greenjacketgirl/SDR_Receiver/Photos/2 - Bit Counter.png

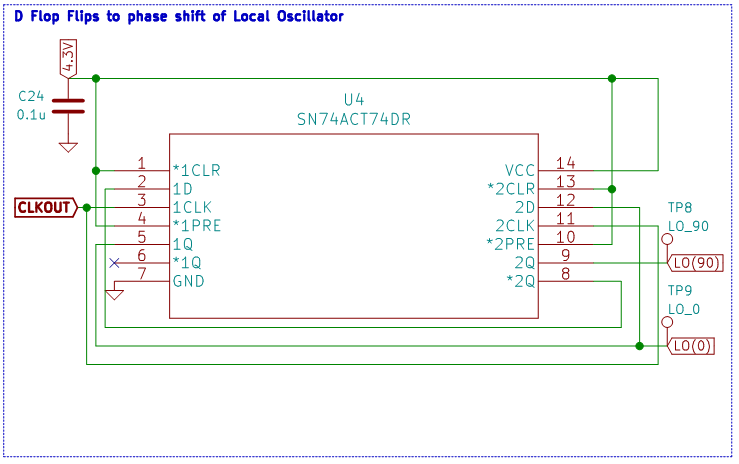
Photos/2 - Bit Counter.png
