greenjacketgirl/SDR_Receiver/Photos/blockdiagramforsdrreceiver.png

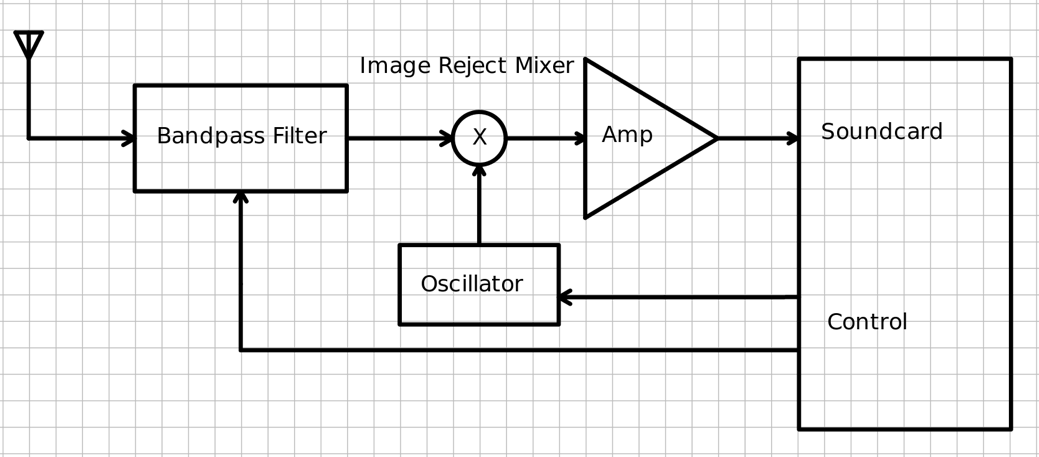
Photos/blockdiagramforsdrreceiver.png
