greenjacketgirl/SDR_Receiver/Photos/IMG_20200519_113151.jpg

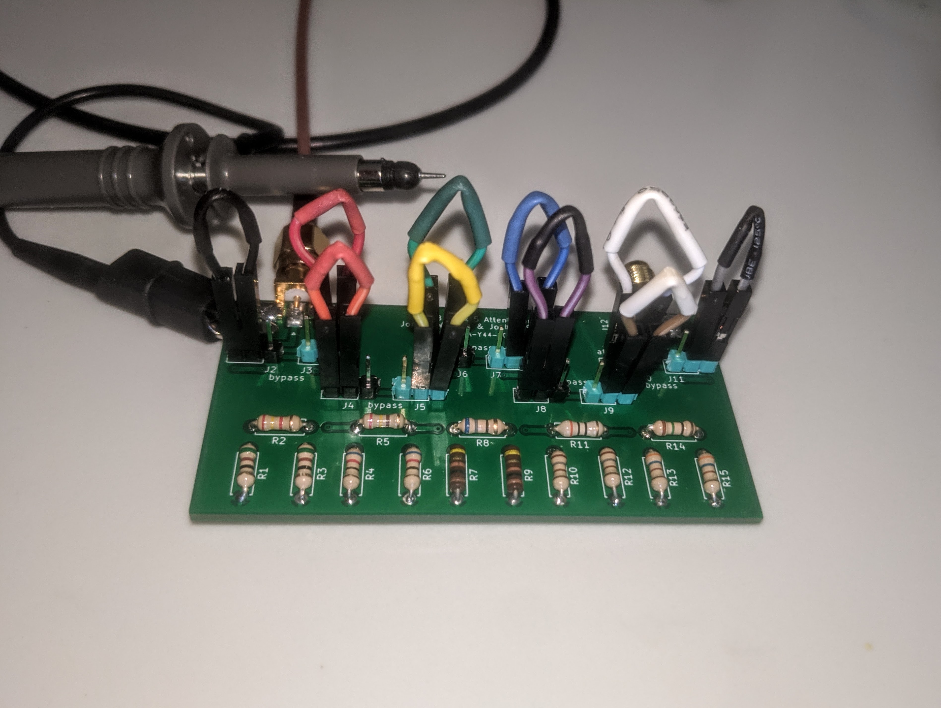
Photos/IMG_20200519_113151.jpg
