greenjacketgirl/SDR_Receiver/Photos/IMG_20200610_005128.jpg

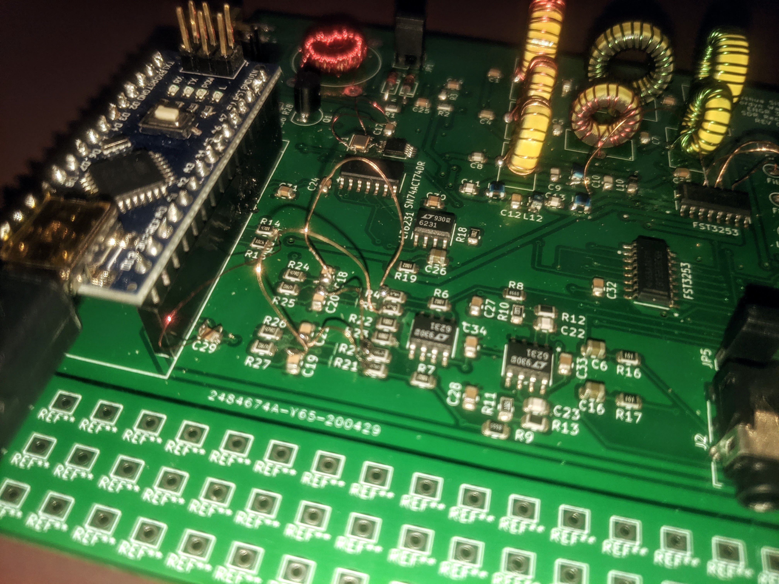
Photos/IMG_20200610_005128.jpg
