greenjacketgirl/SDR_Receiver/Photos/ouputofsummingamps.png

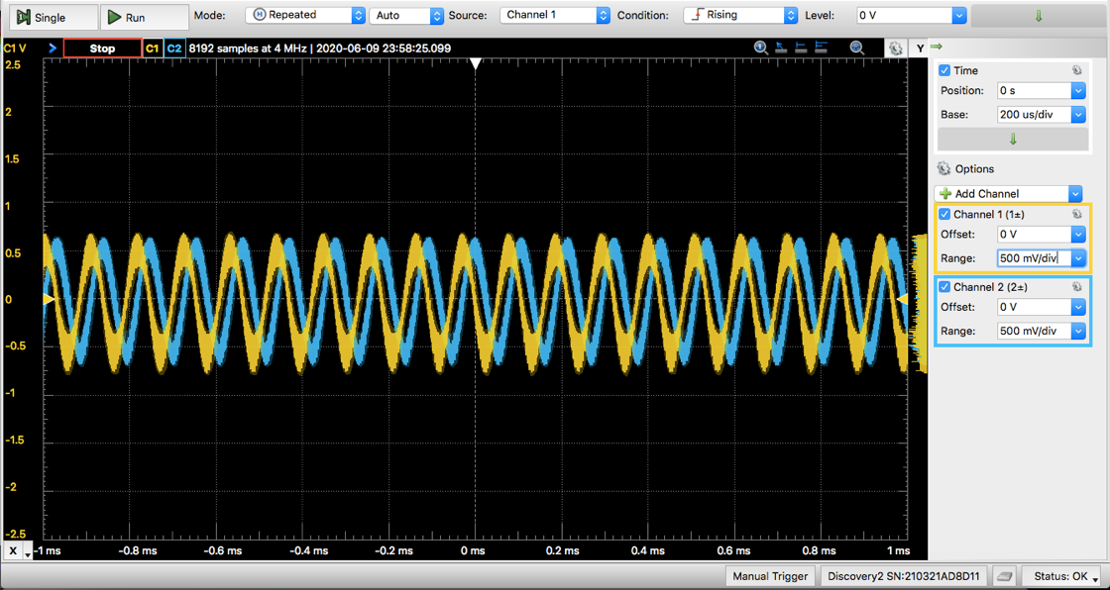
Photos/ouputofsummingamps.png
