greenjacketgirl/SDR_Receiver/Photos/Screenshot 2020-06-01 12.35.27.png

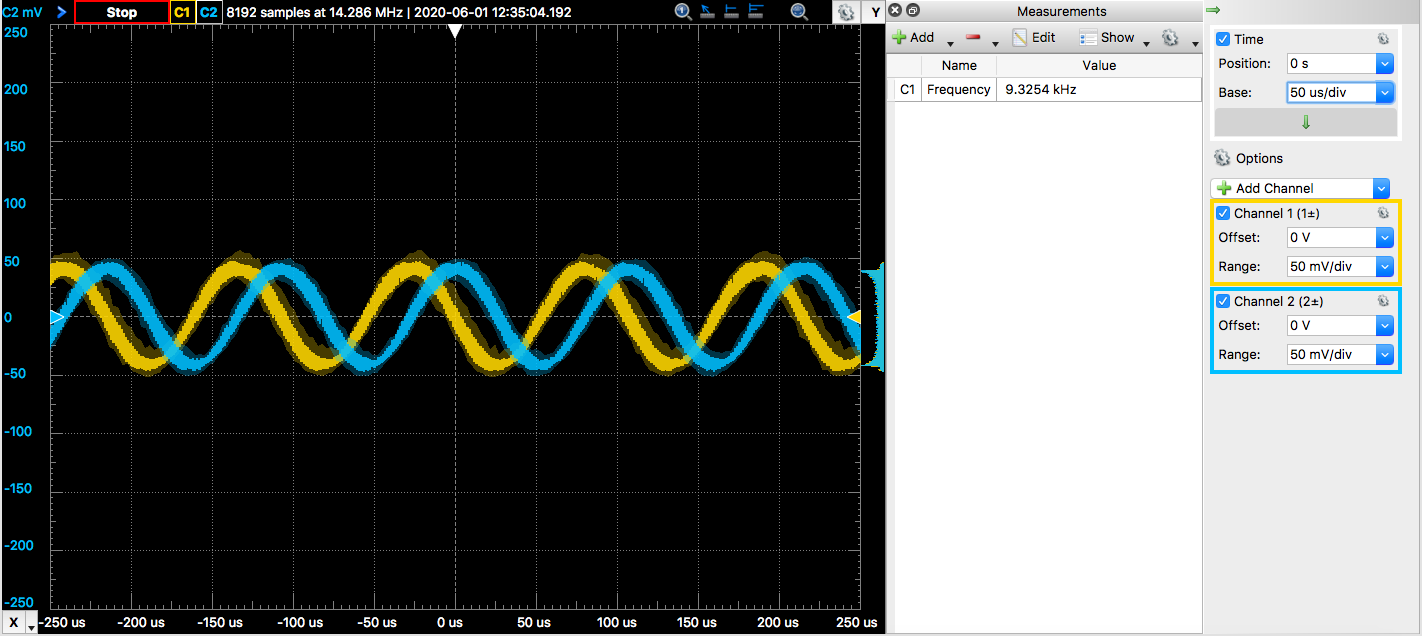
Photos/Screenshot 2020-06-01 12.35.27.png
