greenjacketgirl/SDR_Receiver/Photos/Screenshot 2020-06-01 12.38.04.png

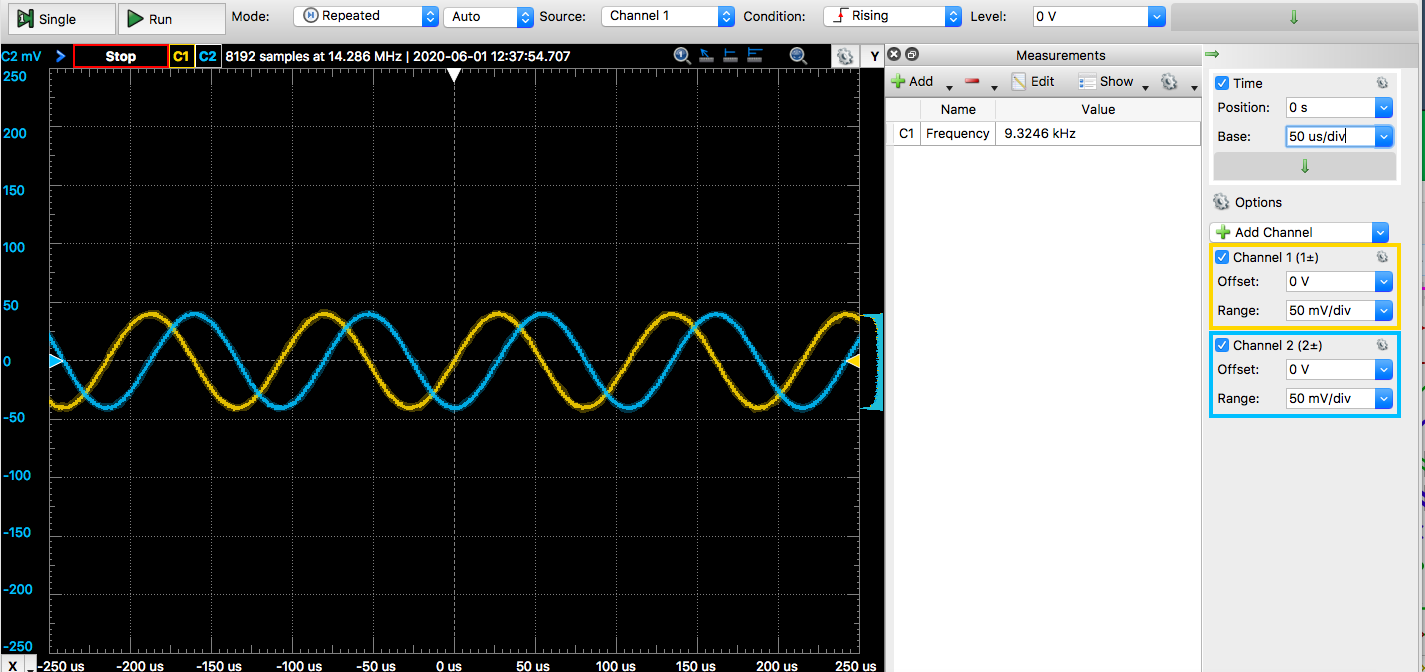
Photos/Screenshot 2020-06-01 12.38.04.png
