greenjacketgirl/SDR_Receiver/Photos/Screenshot 2020-06-01 17.19.47.png

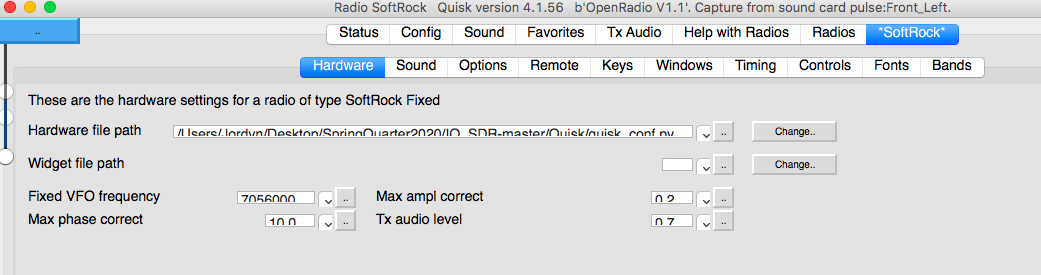
Photos/Screenshot 2020-06-01 17.19.47.png
