greenjacketgirl/SDR_Receiver/Photos/Screenshot 2020-06-03 13.55.31.png

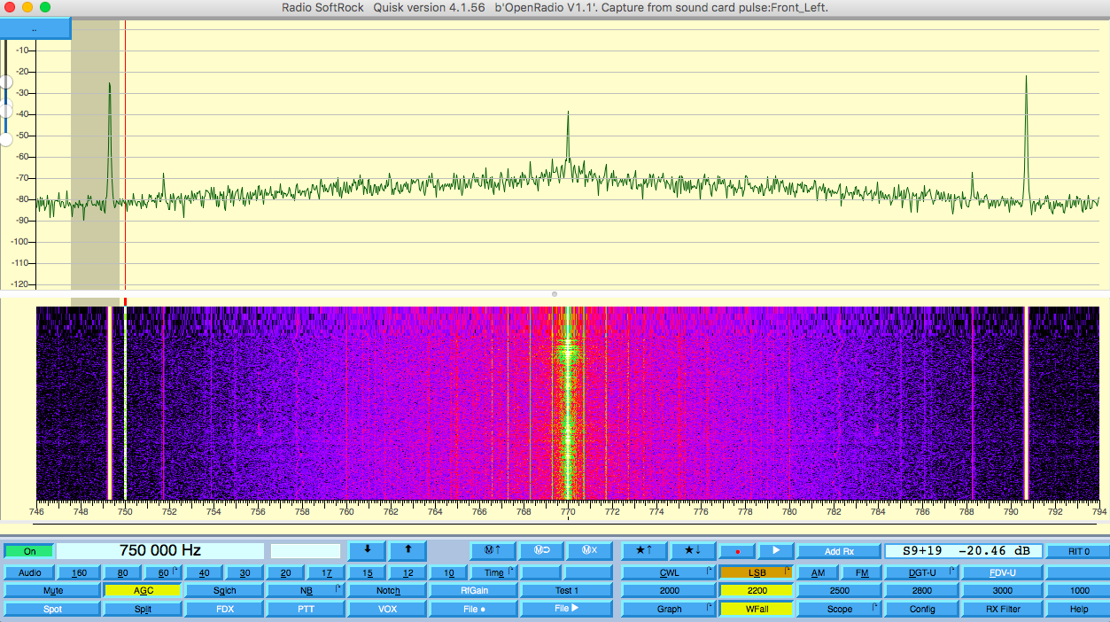
Photos/Screenshot 2020-06-03 13.55.31.png
