greenjacketgirl/SDR_Receiver/Photos/Screenshot 2020-06-03 13.56.09.png

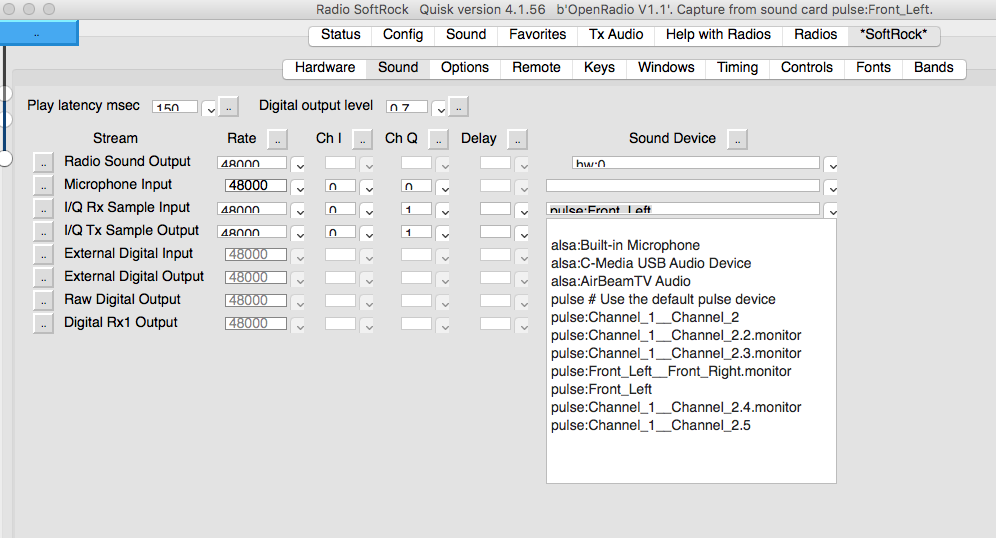
Photos/Screenshot 2020-06-03 13.56.09.png
