greenjacketgirl/SDR_Receiver/Photos/Screenshot 2020-06-05 08.36.38.png

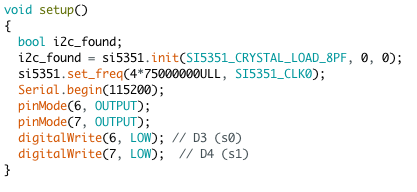
Photos/Screenshot 2020-06-05 08.36.38.png
