greenjacketgirl/SDR_Receiver/Photos/Screenshot 2020-06-09 23.21.12.png

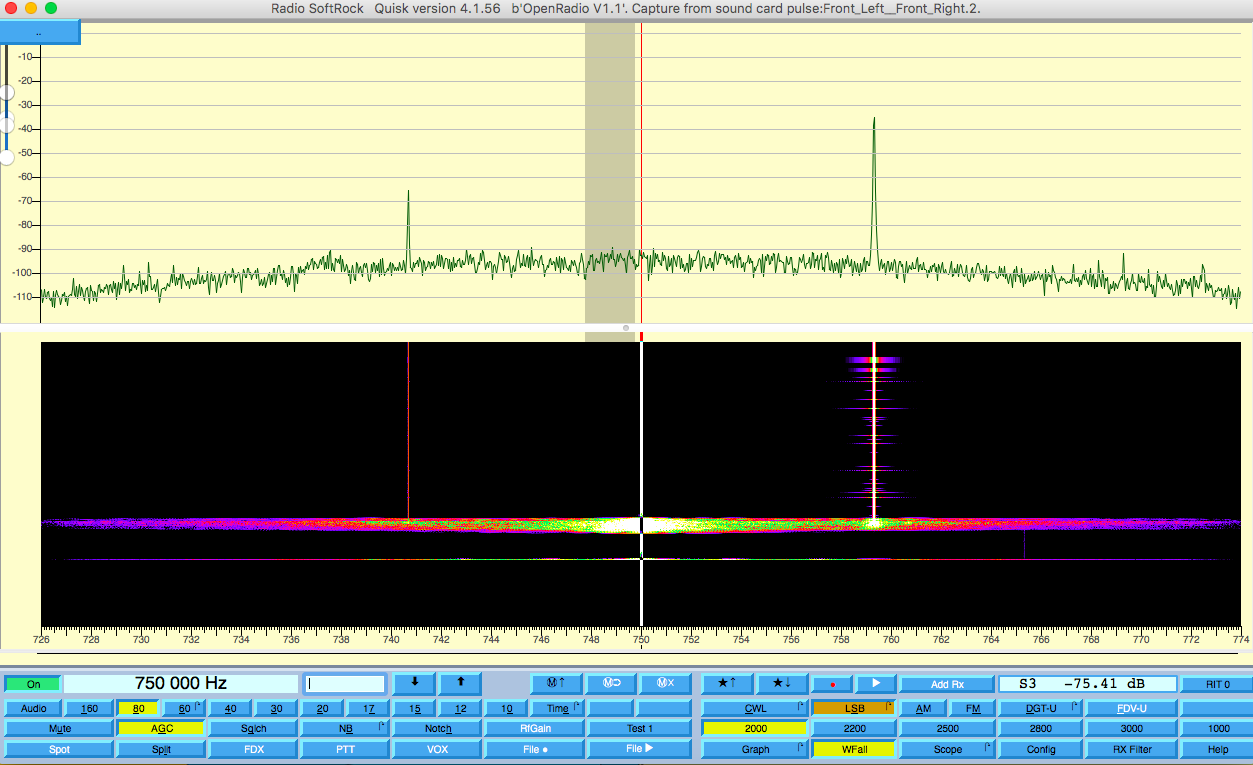
Photos/Screenshot 2020-06-09 23.21.12.png
