greenjacketgirl/SDR_Receiver/Photos/Screenshot 2020-06-09 23.22.24.png

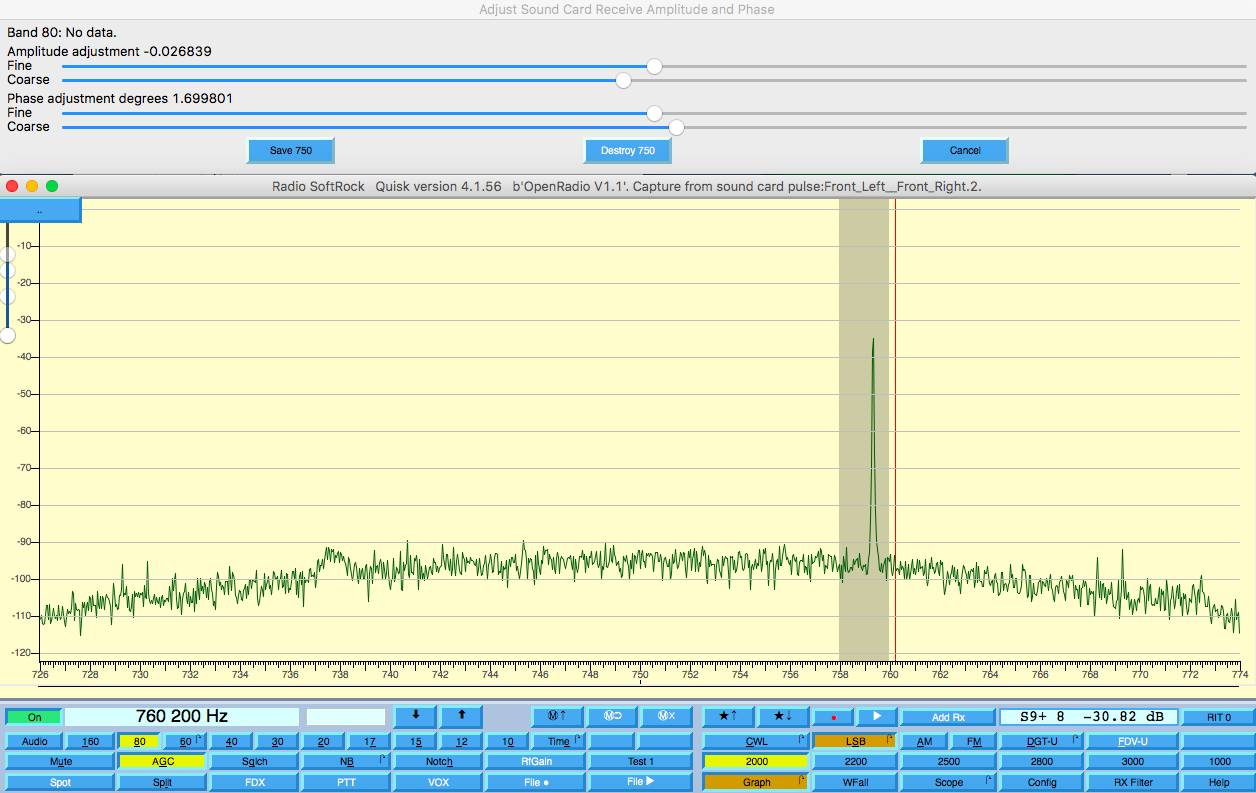
Photos/Screenshot 2020-06-09 23.22.24.png
