greenjacketgirl/SDR_Receiver/Photos/Screenshot 2020-06-09 23.47.44.png

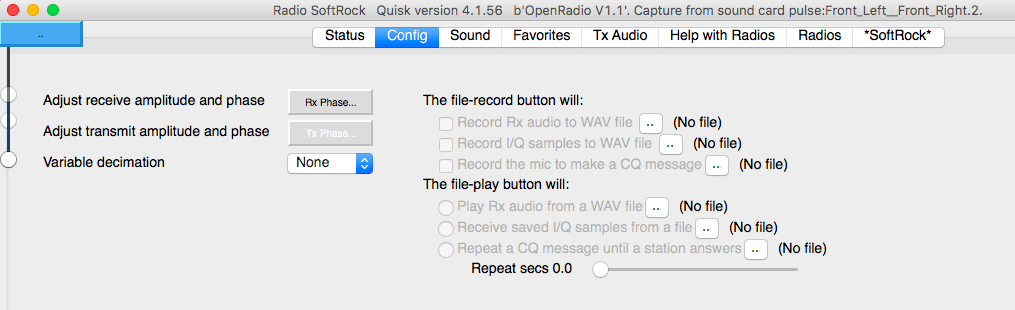
Photos/Screenshot 2020-06-09 23.47.44.png
