greenjacketgirl/SDR_Receiver/Photos/Screenshot 2020-06-09 23.48.01.png

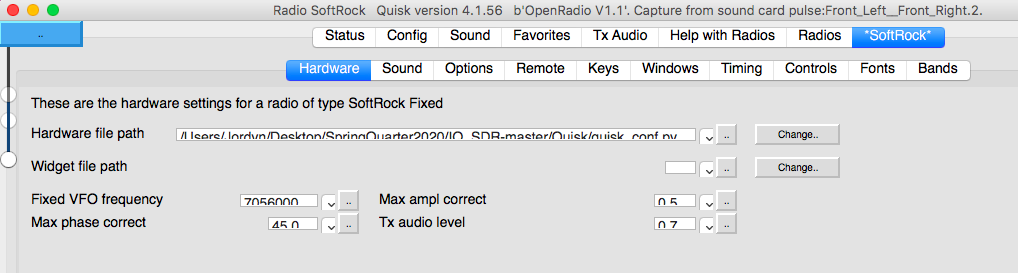
Photos/Screenshot 2020-06-09 23.48.01.png
