greenjacketgirl/SDR_Receiver/Photos/Screenshot 2020-06-10 01.20.28.png

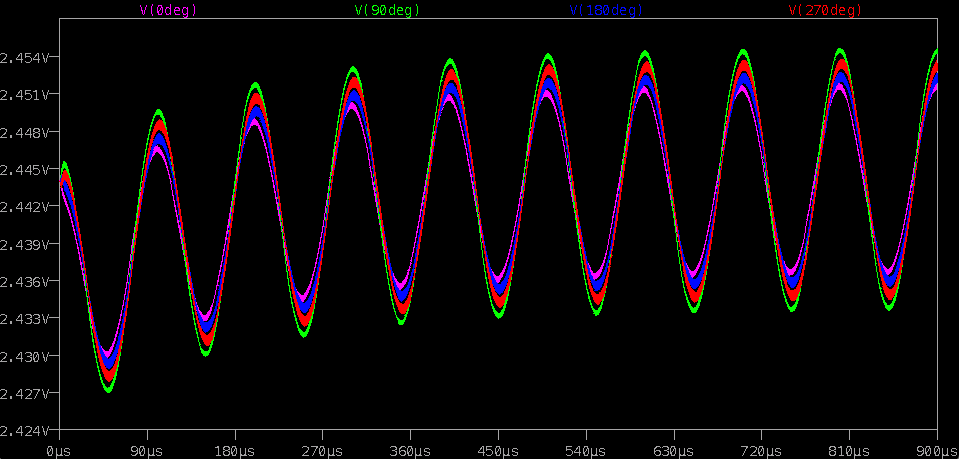
Photos/Screenshot 2020-06-10 01.20.28.png
