greenjacketgirl/SDR_Receiver/Photos/Screenshot 2020-06-10 01.23.52.png

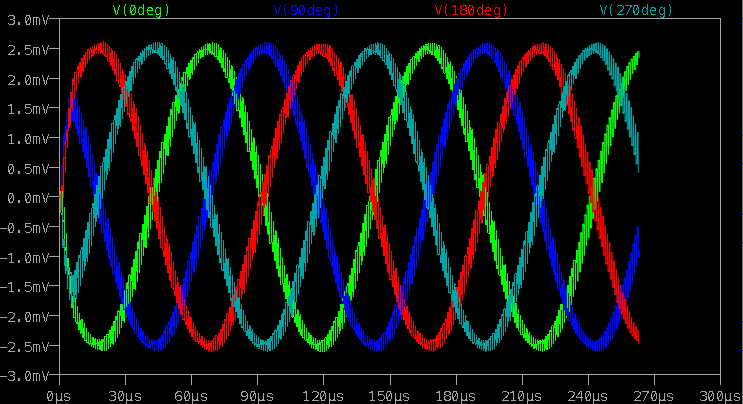
Photos/Screenshot 2020-06-10 01.23.52.png
