greenjacketgirl/SDR_Receiver/Photos/Screenshot 2020-06-11 00.47.50.png

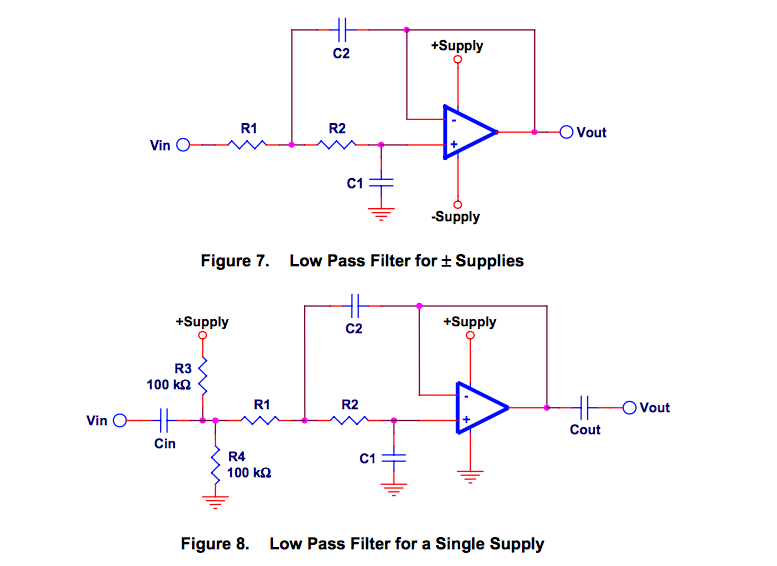
Photos/Screenshot 2020-06-11 00.47.50.png
