greenjacketgirl/SDR_Receiver/Photos/Screenshot 2020-06-11 01.48.22.png

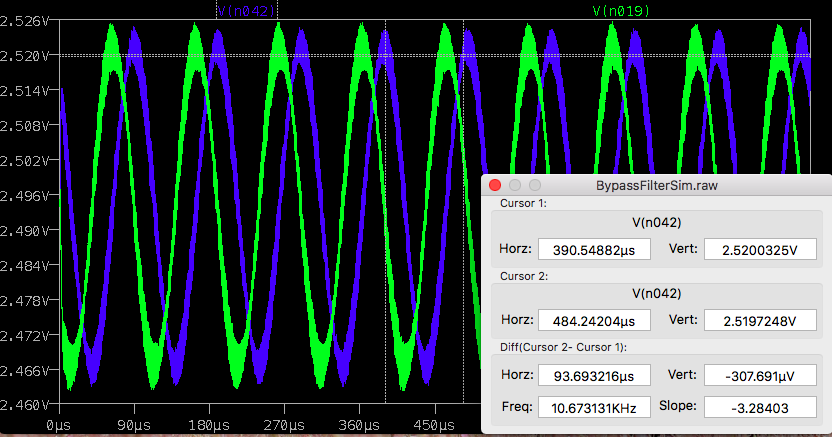
Photos/Screenshot 2020-06-11 01.48.22.png
