greenjacketgirl/SDR_Receiver/Photos/Screenshot 2020-06-11 01.49.03.png

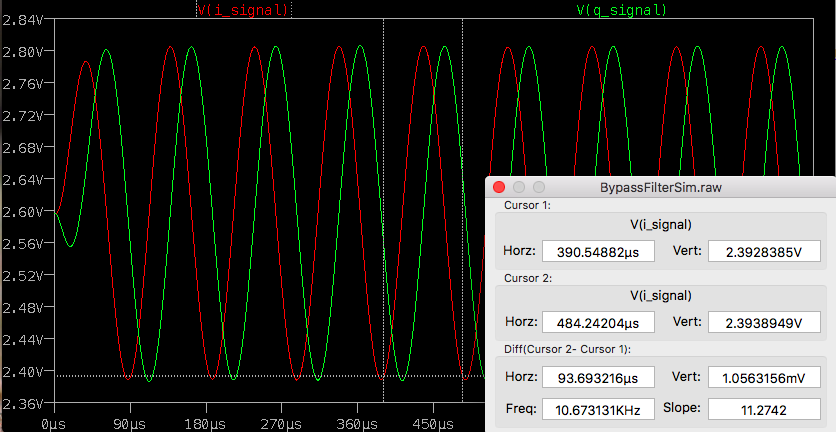
Photos/Screenshot 2020-06-11 01.49.03.png
