greenjacketgirl/SDR_Receiver/Photos/Software Controlled Oscillator.png

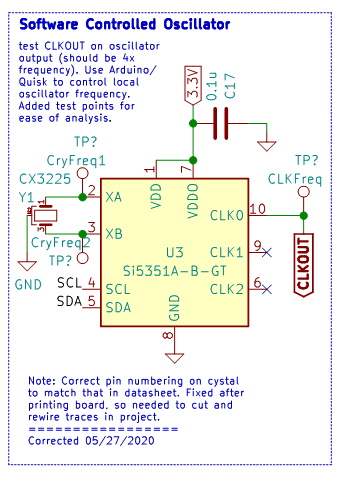
Photos/Software Controlled Oscillator.png
