greenjacketgirl/SDR_Receiver/Photos/Bandpass Filter Results.png

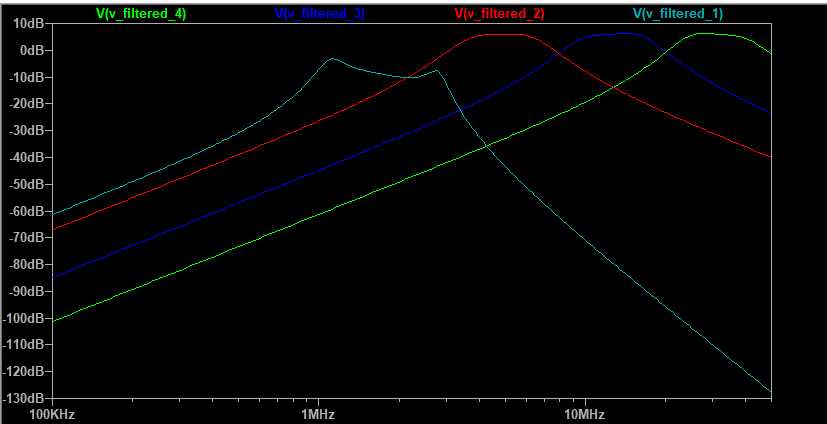
Photos/Bandpass Filter Results.png
