greenjacketgirl/SDR_Receiver/Attenuator/LTSpice/AttenuatorDesignSim.asc

C1: cap; 0.17pF
C2: cap; 0.17pF
C3: cap; 0.17pF
C4: cap; 0.17pF
C5: cap; 0.17pF
C6: cap; 0.17pF
C7: cap; 0.17pF
C8: cap; 0.17pF
C9: cap; 0.17pF
C10: cap; 0.17pF
C11: cap; 0.17pF
C12: cap; 0.17pF
C13: cap; 0.17pF
C14: cap; 0.17pF
C15: cap; 0.17pF
C16: cap; 0.17pF
C17: cap; 0.17pF
C18: cap; 0.17pF
C19: cap; 0.17pF
C20: cap; 0.17pF
R1: res; 51
R2: res; 2.4k
R3: res; 51
R4: res; 62
R5: res; 240
R6: res; 62
R7: res; 100
R8: res; 68
R9: res; 100
R10: res; 180
R11: res; 30
R12: res; 180
R13: res; 360
R14: res; 15
R15: res; 360
R16: res; 360
R17: res; 15
R18: res; 360
R19: res; 180
R20: res; 30
R21: res; 180
R22: res; 50
R23: res; 100
R24: res; 50
R25: res; 68
R26: res; 100
R27: res; 62
R28: res; 640
R29: res; 62
R30: res; 51
R31: res; 2.4K
R32: res; 51
R34: res; 50
V1: voltage; SINE(0 2 1k); AC 5m
V2: voltage; SINE(0 2 1k); AC 5m
Named nets: 0
;.ac DEC 100 31MEG 300MEG
.tran 1m
;.op
40 dB
20dB
10dB
5dB
2.5dB
40 dB
20dB
10dB
5dB
2.5dB
