greenjacketgirl/SDR_Receiver/SDR Receiver/LTSPICE/TayloeMixerSim.asc

C1: cap; .82µ
C2: cap; .82µ
C3: cap; .82µ
C4: cap; .82µ
C5: cap; 100p
C6: cap; 100p
R1: res; 200
R2: res; 10k
R3: res; 10k
R4: res; 100
R5: res; 100
R6: res; 100
R7: res; 100
S1: sw
S2: sw
S3: sw
S4: sw
S5: sw
S6: sw
S7: sw
S8: sw
U1: LT1115
U2: LT1115
V1: voltage; PULSE(-1 1 8.75e-7 0 0 2.5e-7 1e-6)
V2: voltage; PULSE(-1 1 6.25e-7 0 0 2.5e-7 1e-6)
V3: voltage; PULSE(-1 1 3.75e-7 0 0 2.5e-7 1e-6)
V4: voltage; PULSE(-1 1 8.75e-7 0 0 2.5e-7 1e-6)
V5: voltage; PULSE(-1 1 6.25e-7 0 0 2.5e-7 1e-6)
V6: voltage; PULSE(-1 1 3.75e-7 0 0 2.5e-7 1e-6)
V7: voltage; PULSE(-1 1 1.25e-7 0 0 2.5e-7 1e-6)
V8: voltage; PULSE(-1 1 1.25e-7 0 0 2.5e-7 1e-6)
V9: voltage; SINE(0 0.5u 3MEG)
V11: voltage; 5
Named nets: 0, Q, I, N002, N004, N011, N014
0 deg
90 deg
180 deg
270 deg
.model SW SW(Ron=1 Roff=1MEG Vt=0 Vh=0)
.tran 0 1m 0.5u 1u
0 deg
90 deg
180 deg
270 deg
Gain of 100 on Op-Amps from 
resistors R3, R4 and R2,R7:
Av= (1+ R3/R4)
Note: Add decoupling capacitors in 
series with R4, R5, R6, R7, and a voltage divider to have dc offset
going into op-amp of 2.5V
